epgodoy/ID7780-ieeelatam/Invólucro/Foto 3.JPG

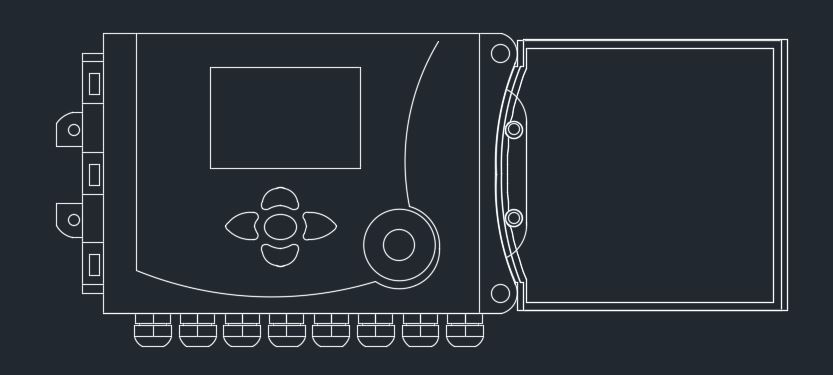
Invólucro/Foto 3.JPG
